chaos-consulting/adsberry/3dfiles/images/IMG_20210603_150542.jpg

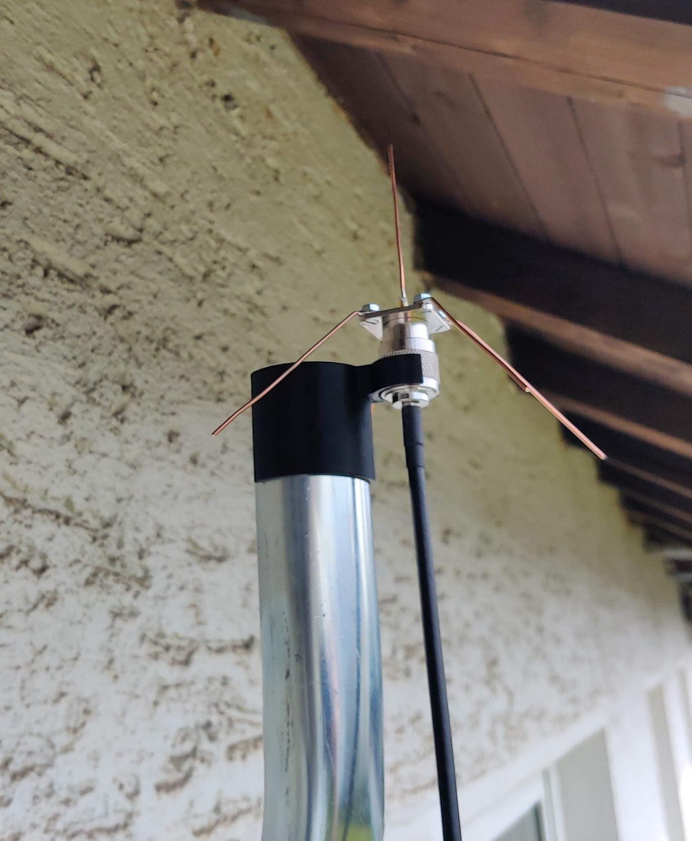
3dfiles/images/IMG_20210603_150542.jpg
