chaos-consulting/adsberry/3dfiles/images/IMG_20210603_150830.jpg

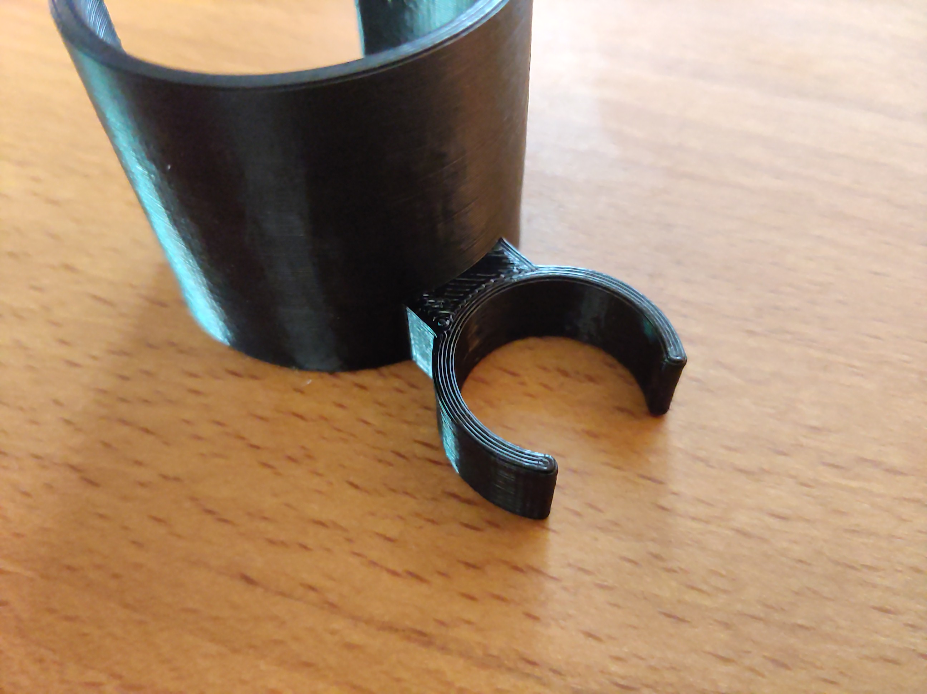
3dfiles/images/IMG_20210603_150830.jpg
