chaos-consulting/adsberry/3dfiles/images/IMG_20210603_214528.jpg

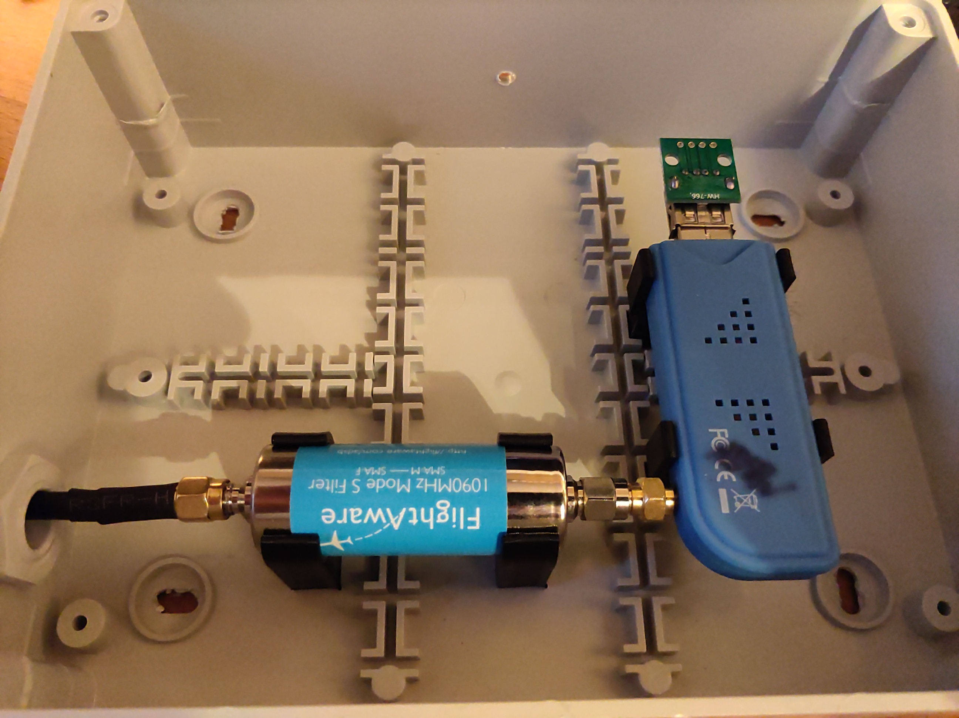
3dfiles/images/IMG_20210603_214528.jpg
