chaos-consulting/adsberry/3dfiles/images/IMG_20210612_011027.jpg

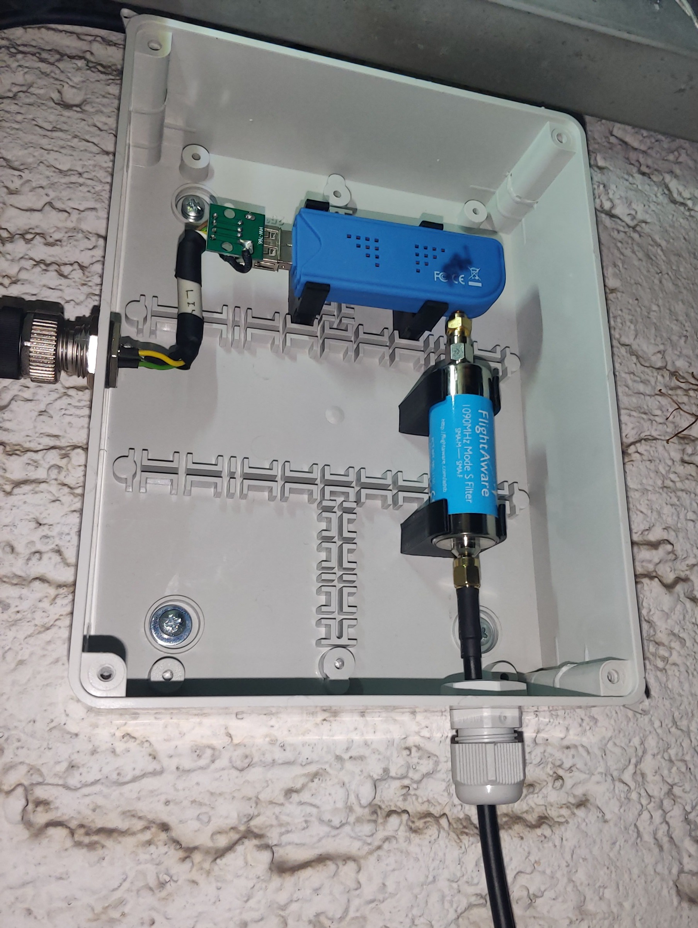
3dfiles/images/IMG_20210612_011027.jpg
