chaos-consulting/adsberry/antennas/gp07.jpg

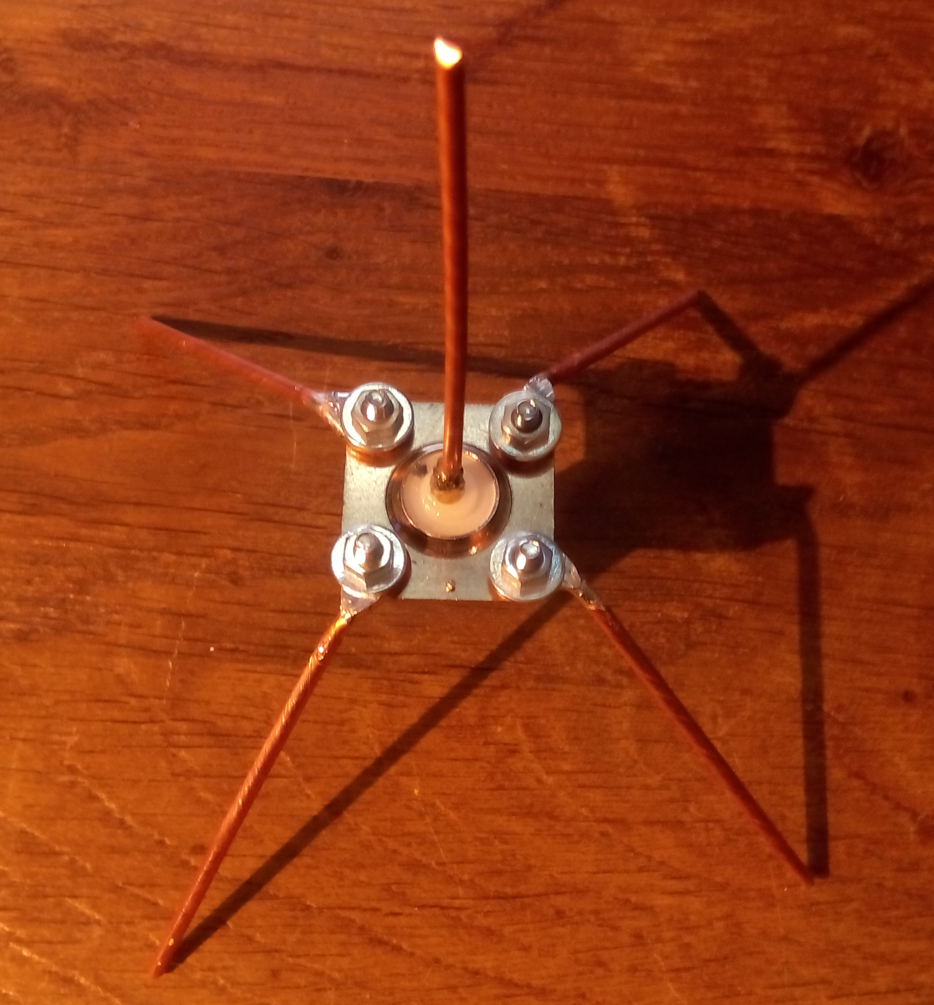
antennas/gp07.jpg
