chaos-consulting/adsberry/antennas/gp08.jpg

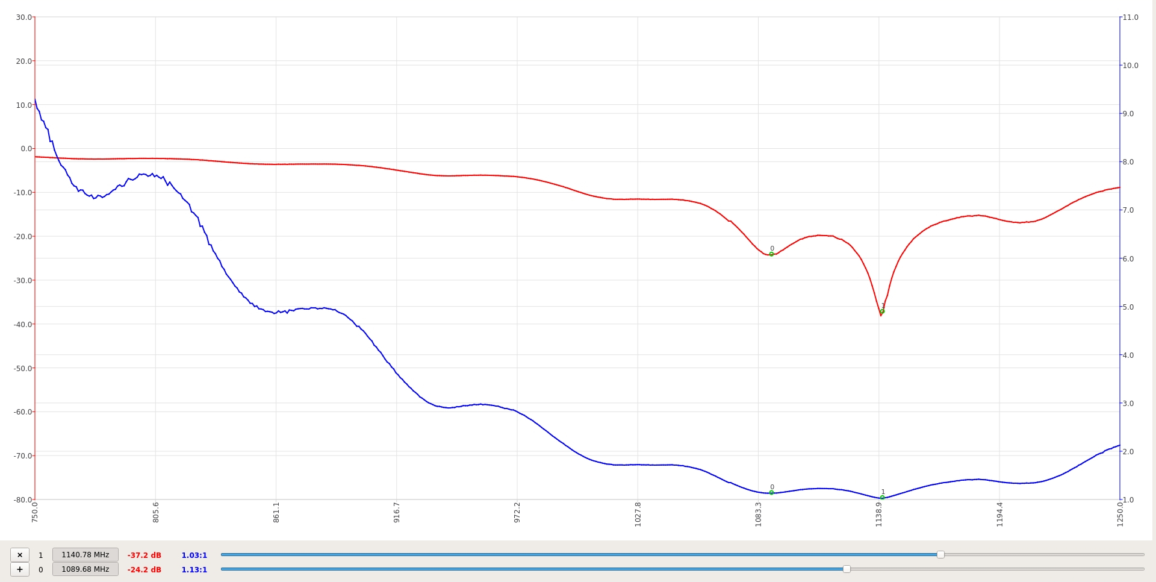
antennas/gp08.jpg
