chaos-consulting/adsberry/antennas/pcb07.jpg

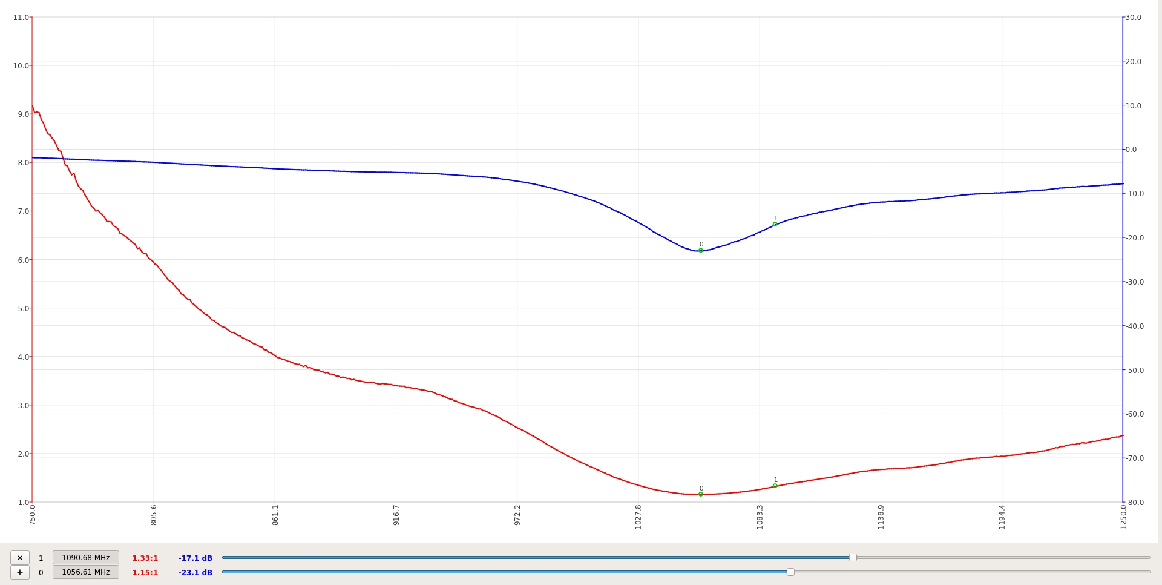
antennas/pcb07.jpg
