chaos-consulting/adsberry/filters/airnavvna.jpg

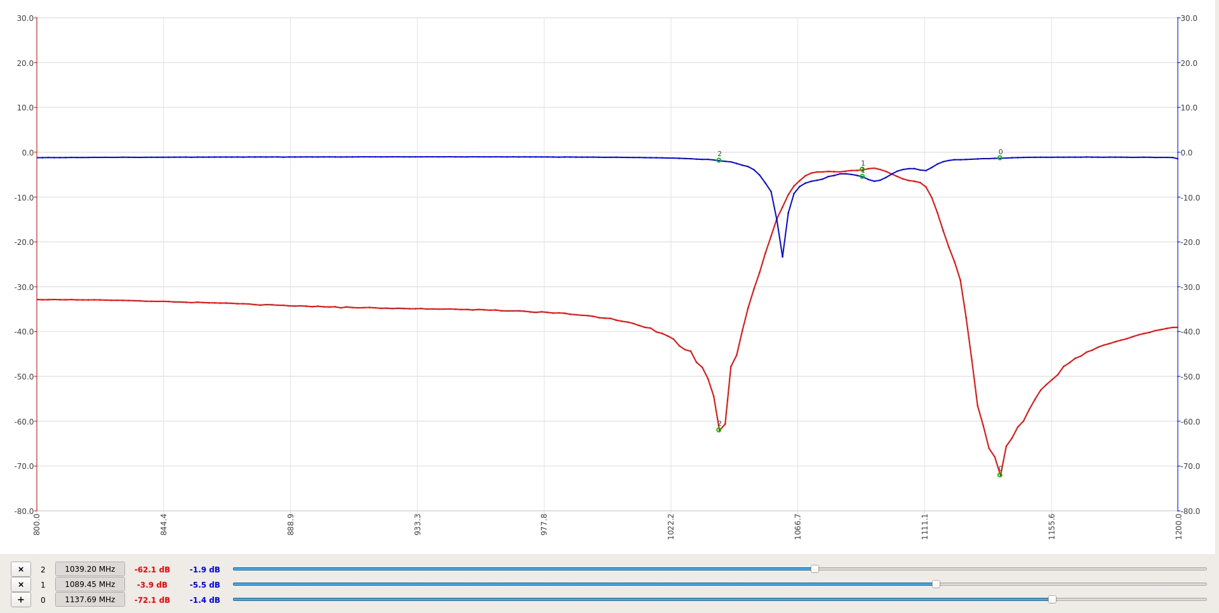
filters/airnavvna.jpg
