chaos-consulting/adsberry/filters/fa-dualband-vna.jpg

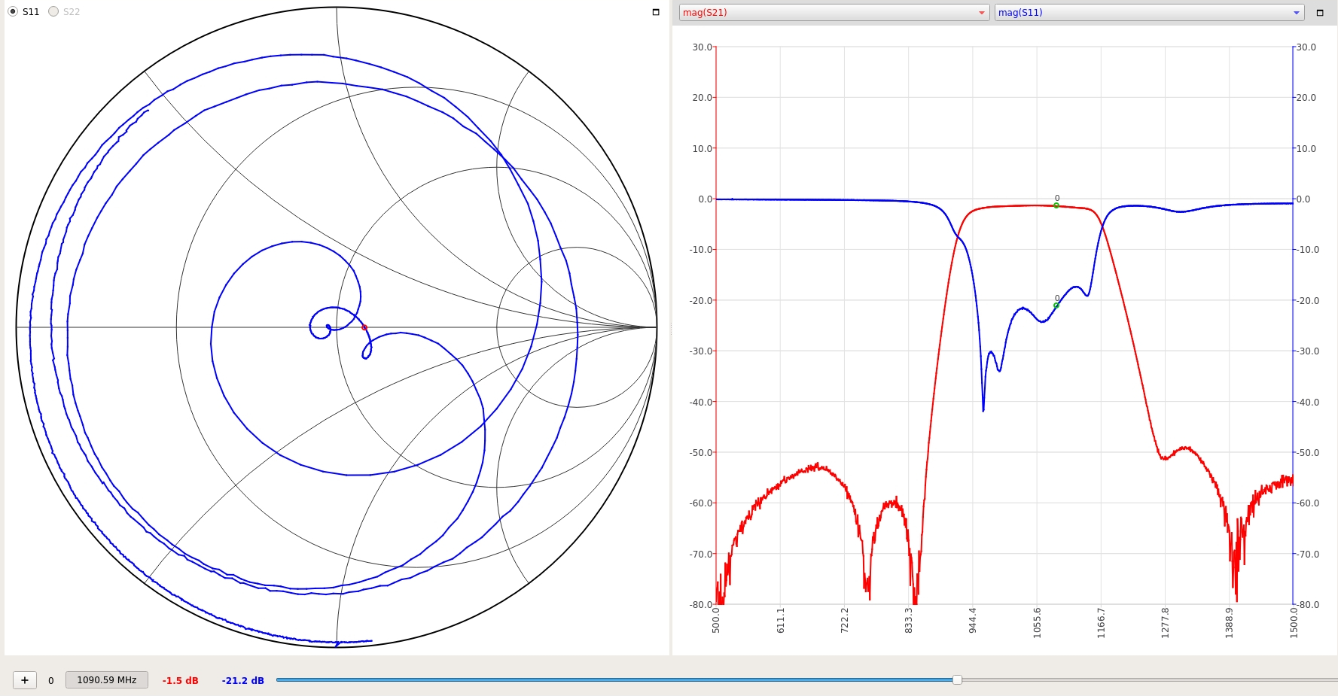
filters/fa-dualband-vna.jpg
