chaos-consulting/adsberry/filters/fa-dualband.jpg

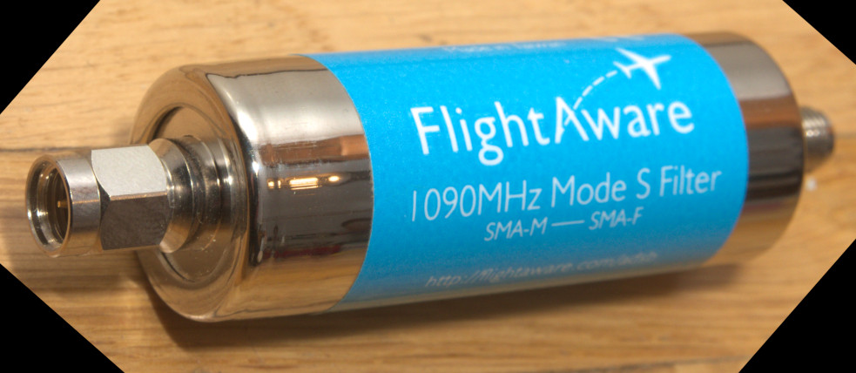
filters/fa-dualband.jpg
