chaos-consulting/adsberry/filters/fa-singleband.jpg

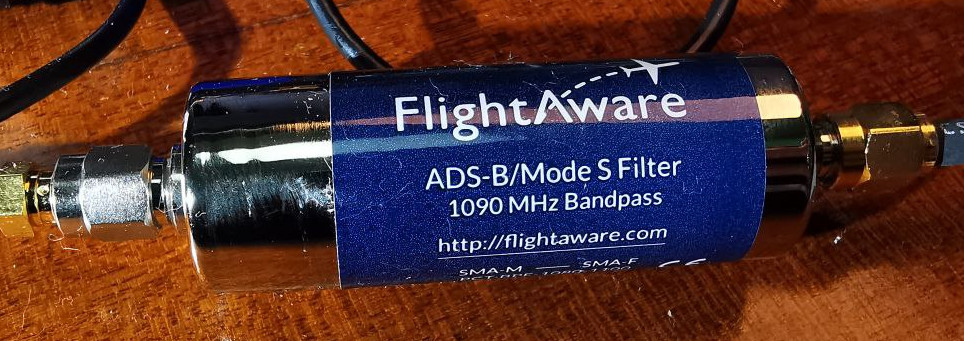
filters/fa-singleband.jpg
