chaos-consulting/adsberry/filters/radarbox-filter.jpg

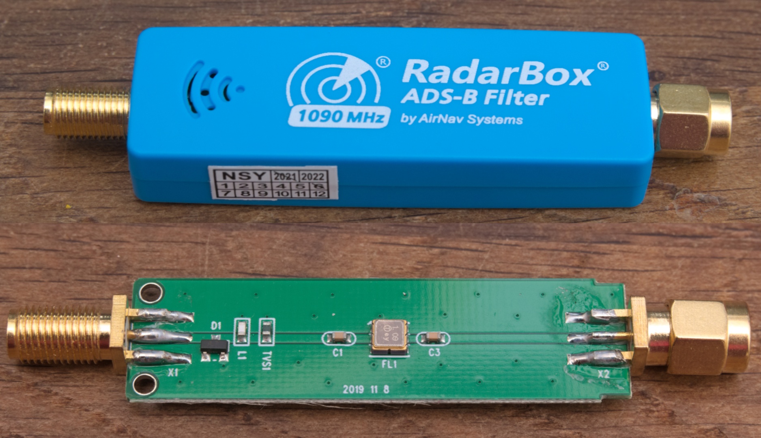
filters/radarbox-filter.jpg
