chaos-consulting/adsberry/lnas/LnaSpf5189Z-5To6000-20db.jpg

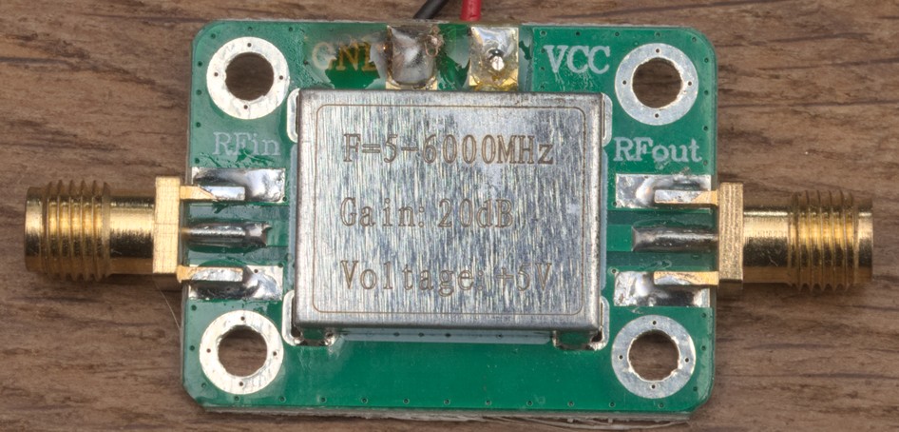
lnas/LnaSpf5189Z-5To6000-20db.jpg
