chaos-consulting/adsberry/lnas/NooelecLanaV2.jpg

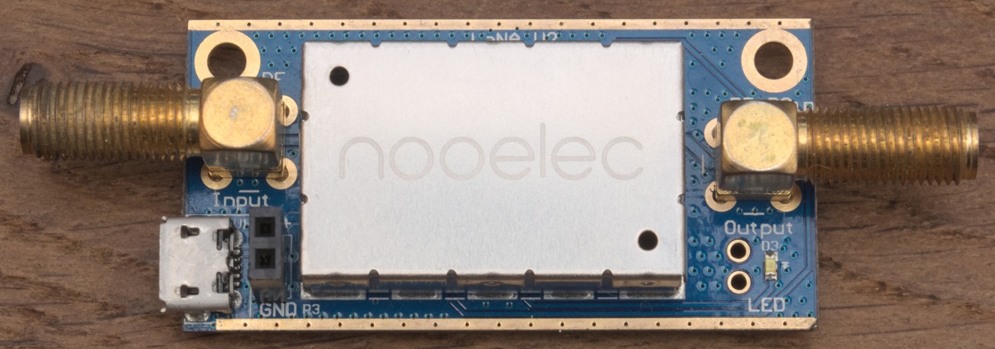
lnas/NooelecLanaV2.jpg
