chaos-consulting/adsberry/sticks/FlightAwareProStick.jpg

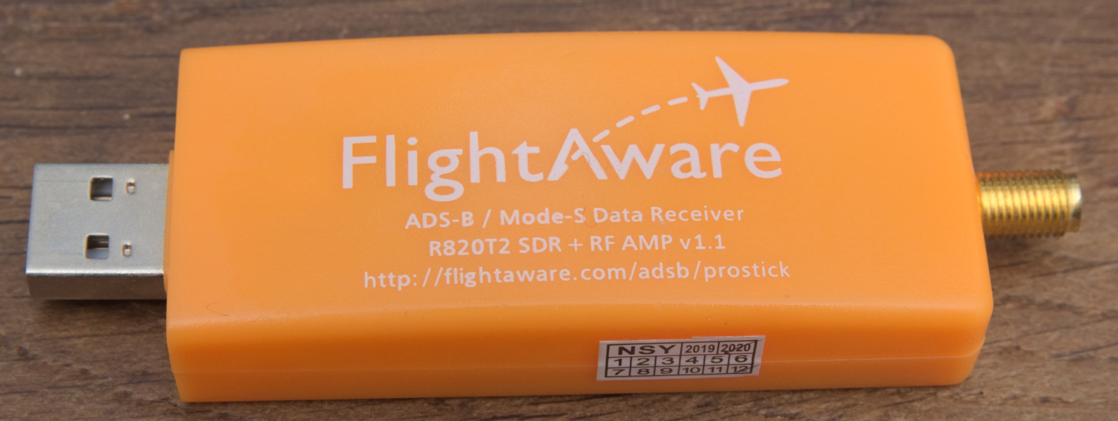
sticks/FlightAwareProStick.jpg
