chaos-consulting/adsberry/sticks/FlightAwareProStickPlus.jpg

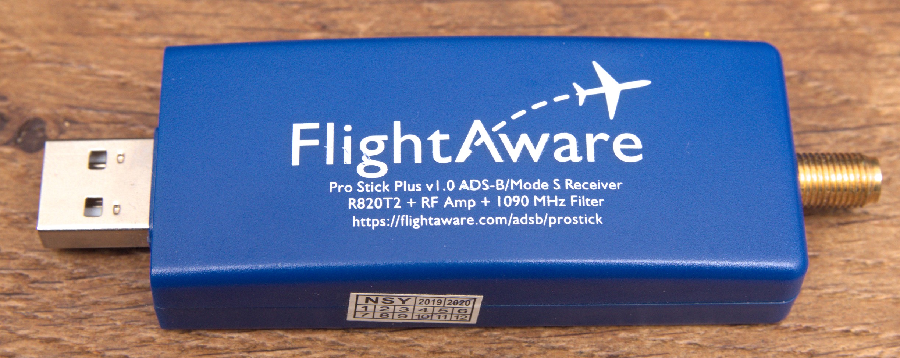
sticks/FlightAwareProStickPlus.jpg
