chaos-consulting/adsberry/sticks/generic.jpg

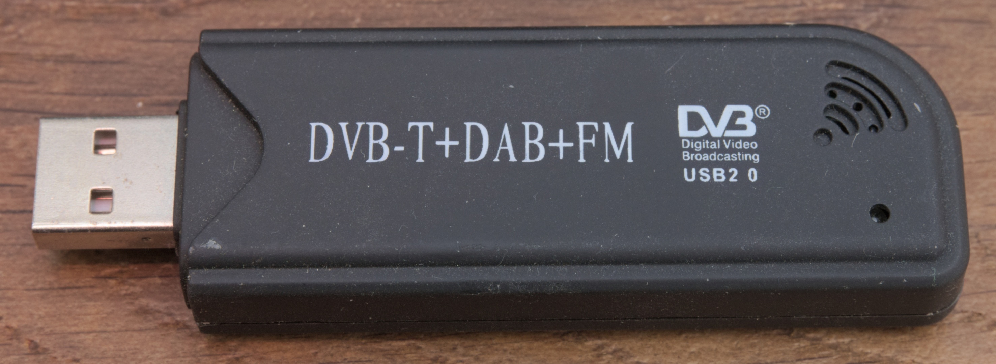
sticks/generic.jpg
