chaos-consulting/adsberry/sticks/NooelecNanoV3.jpg

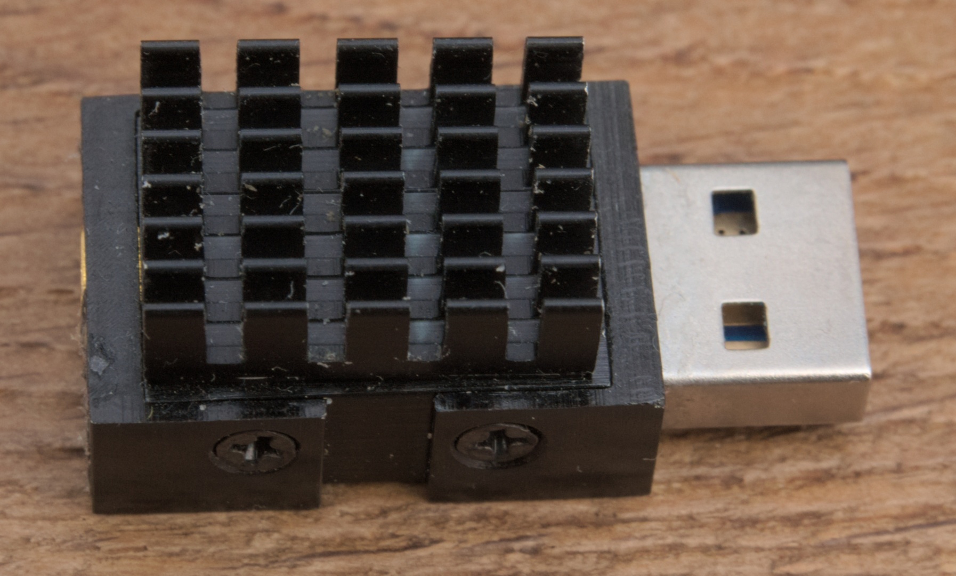
sticks/NooelecNanoV3.jpg
