chaos-consulting/adsberry/sticks/NooelecNESDRSMArtee.jpg

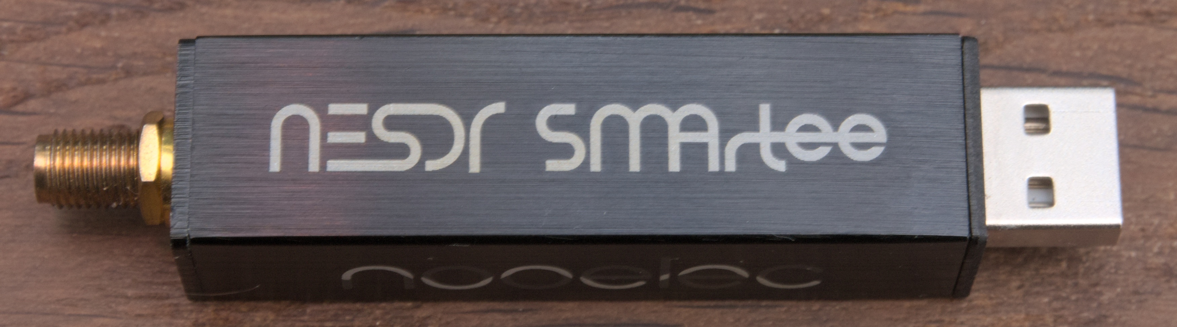
sticks/NooelecNESDRSMArtee.jpg
