chaos-consulting/adsberry/sticks/NooelecNESDRSMArtv5.jpg

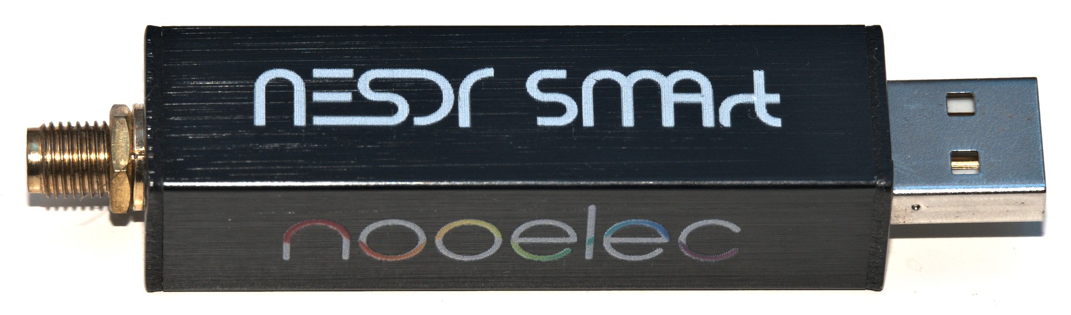
sticks/NooelecNESDRSMArtv5.jpg
