chaos-consulting/adsberry/sticks/RadarBoxFlightStick.jpg

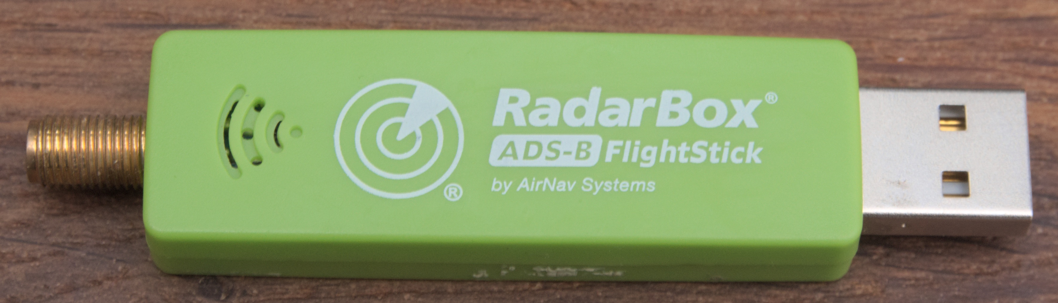
sticks/RadarBoxFlightStick.jpg
