chaos-consulting/adsberry/sticks/RtlSdrComV3.jpg

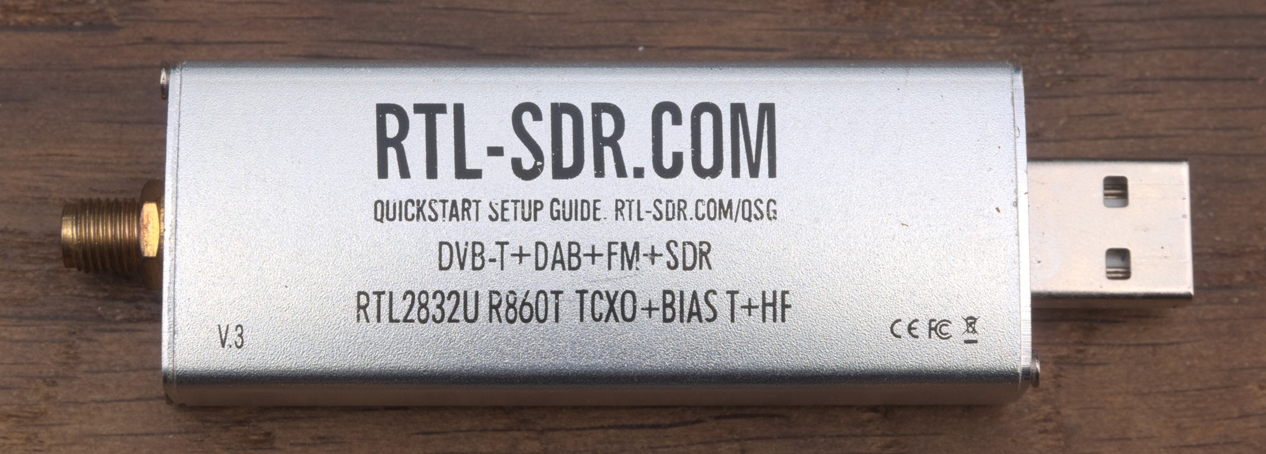
sticks/RtlSdrComV3.jpg
