chaos-consulting/adsberry/sticks/RtlSdrComV3blk.jpg

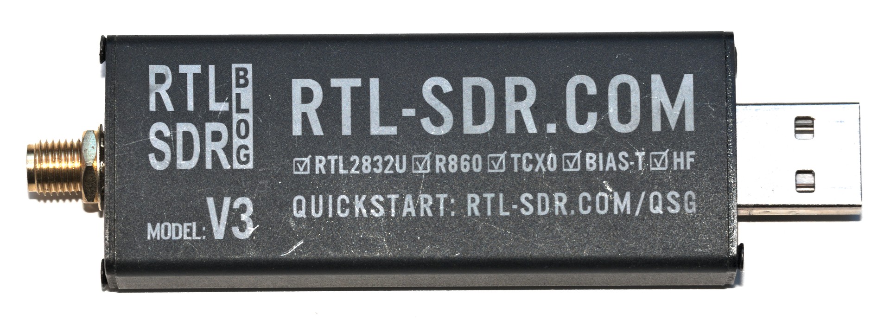
sticks/RtlSdrComV3blk.jpg
