chaos-consulting/adsberry/sticks/ShipXplorer.jpg

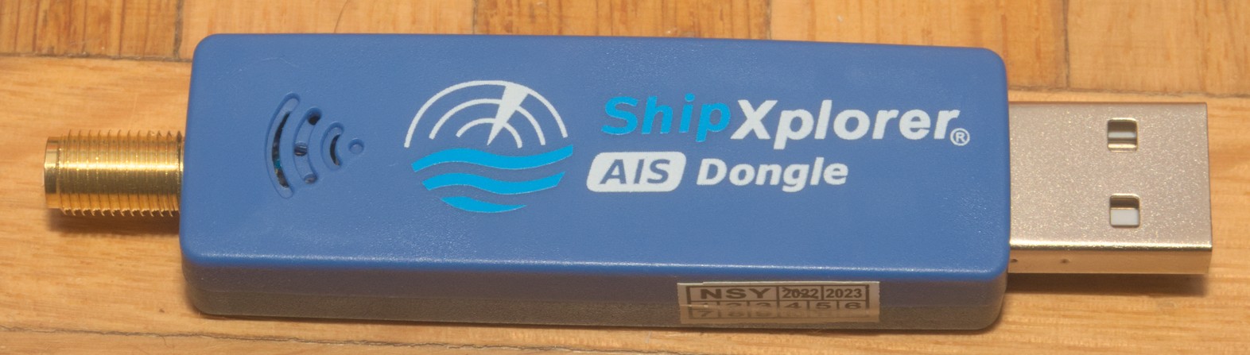
sticks/ShipXplorer.jpg
