chaos-consulting/adsberry/sticks/ShipXplorerOpen.jpg

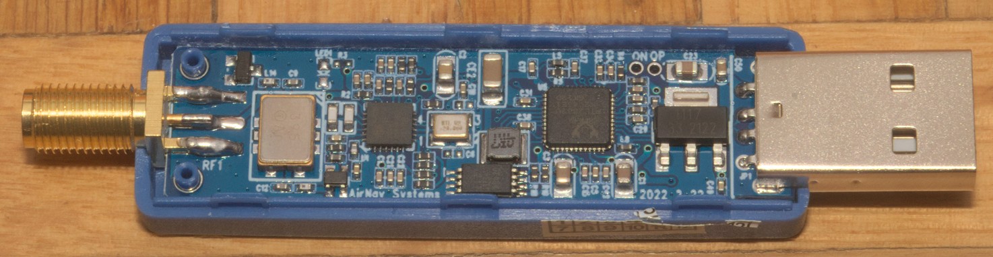
sticks/ShipXplorerOpen.jpg
