chaos-consulting/adsberry/sticks/ShipXplorerRTL.jpg

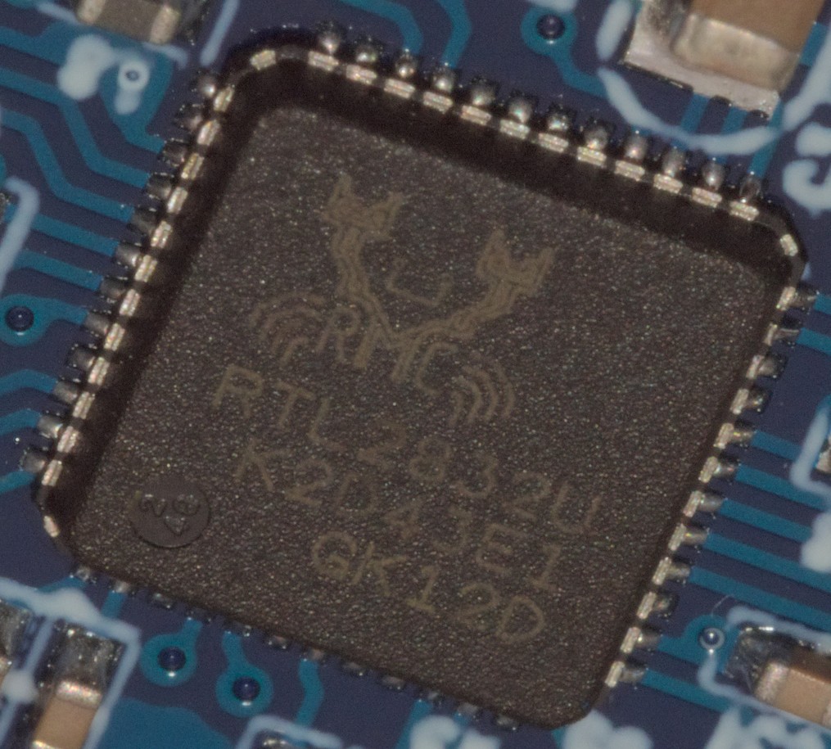
sticks/ShipXplorerRTL.jpg
