chaos-consulting/adsberry/sticks/ShipXplorerTuner.jpg

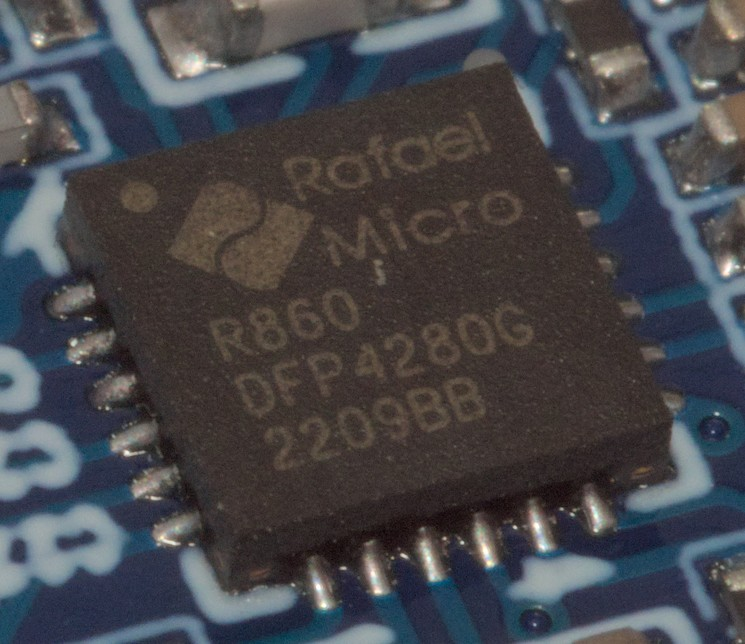
sticks/ShipXplorerTuner.jpg
